Allen953/HotDog/1.3D model/HotDog/LB_SHANK_LINK.SLDASM

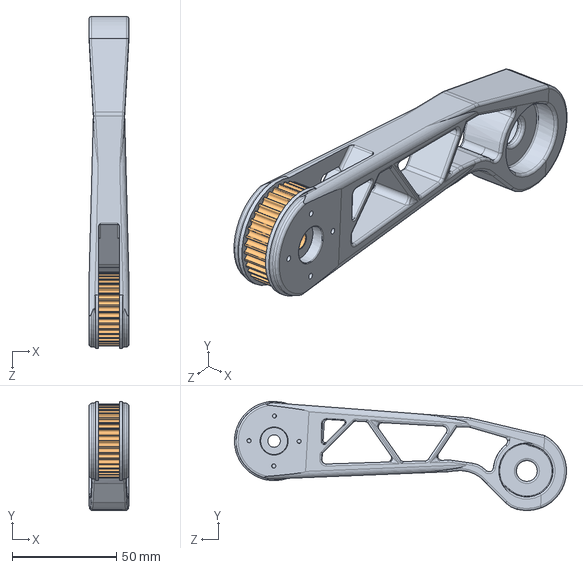
[picture p50: CAD file, 2022-09-22]
1.3D model/HotDog/LB_SHANK_LINK.SLDASM
19.0 x 52.3 x 159.1 mm
小足
同步轮
