Allen953/HotDog/1.3D model/HotDog/LB_THIGH_LINK.SLDASM

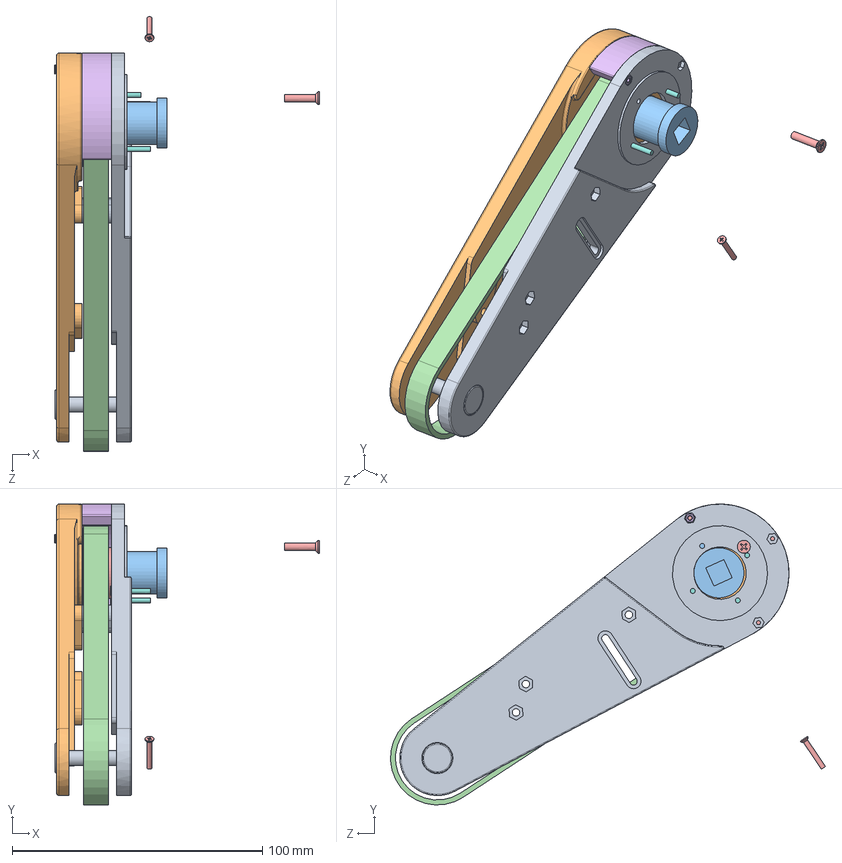
[picture p51: CAD file, 2022-09-22]
1.3D model/HotDog/LB_THIGH_LINK.SLDASM
105.9 x 120.3 x 173.9 mm
大足
大足2
光杆同步轮
同步带
cross recessed countersunk head screws gb1 x 5
hex nuts, style 1-grades ab gb
端盖
cross countersunk head screw_as x 4
字母钉
17-23-4轴承 x 2
传动轴
定位环_17_20_1-2mm
定位环
支撑半环
