Allen953/HotDog/1.3D model/HotDog/定位环_17_20_1-2mm.SLDPRT

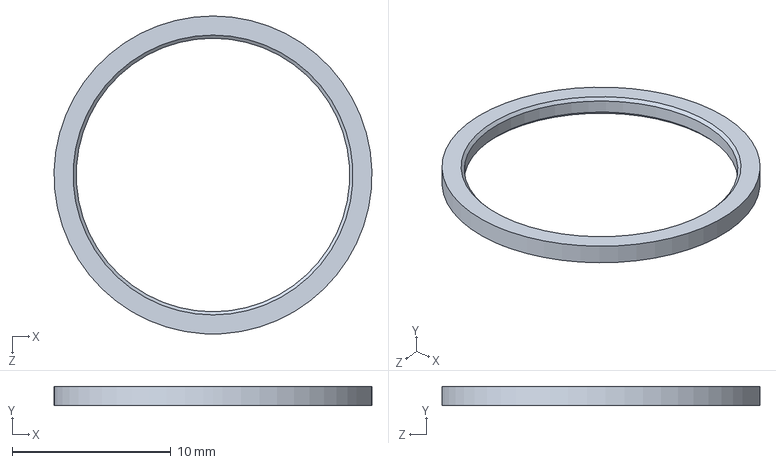
[picture p52: CAD file, 2022-09-22]
1.3D model/HotDog/定位环_17_20_1-2mm.SLDPRT
20.0 x 1.20 x 20.0 mm
