Allen953/HotDog/3.Software/ROS package/HotDog/meshes/LF_R_LINK.STL

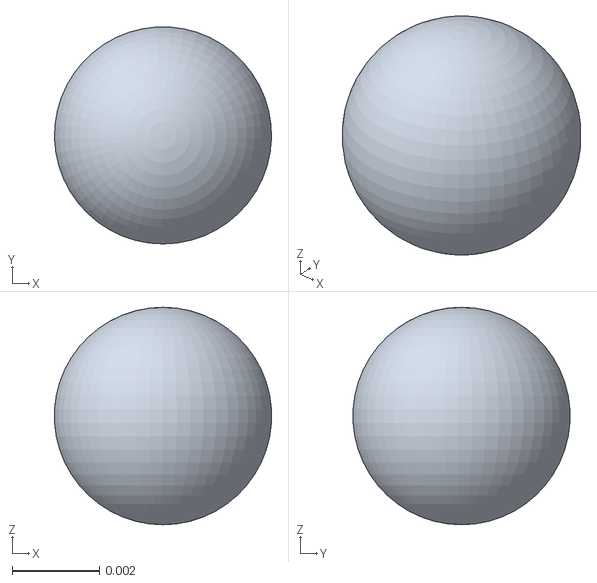
[picture p53: CAD file, 2022-09-22]
3.Software/ROS package/HotDog/meshes/LF_R_LINK.STL
0.00499 x 0.00499 x 0.005
