Allen953/HotDog/1.3D model/HotDog/小足.SLDPRT

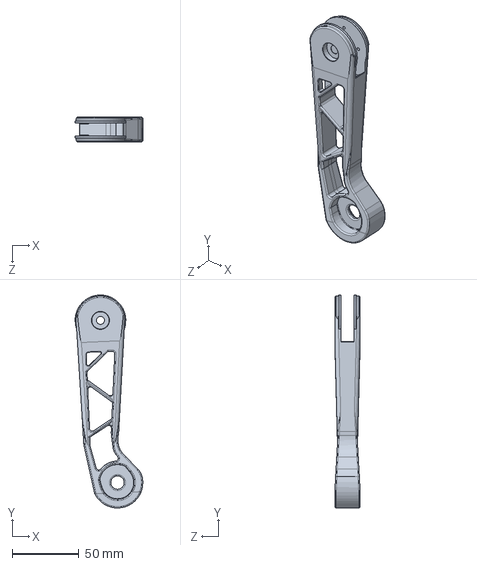
[picture p54: CAD file, 2022-09-22]
1.3D model/HotDog/小足.SLDPRT
50.7 x 159.3 x 19.0 mm
