Allen953/HotDog/3.Software/ROS package/HotDog/meshes/RB_JIAN_LINK.STL

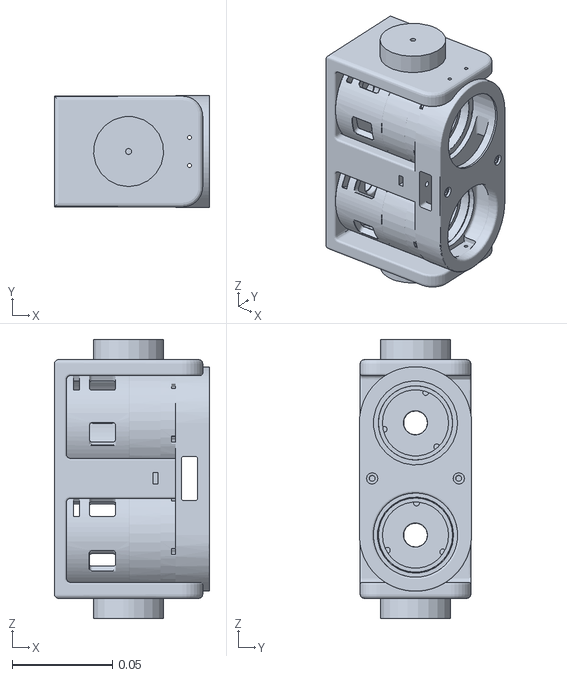
[picture p55: CAD file, 2022-09-22]
3.Software/ROS package/HotDog/meshes/RB_JIAN_LINK.STL
0.0774 x 0.056 x 0.139
