Allen953/HotDog/1.3D model/HotDog/定位环.SLDPRT

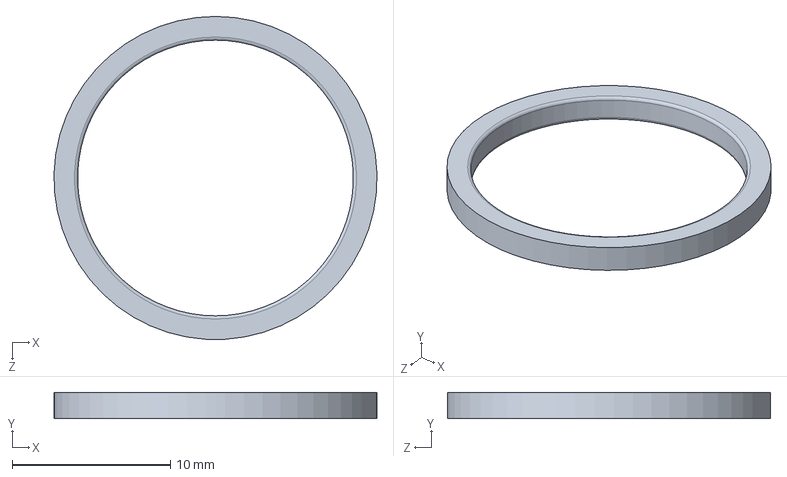
[picture p56: CAD file, 2022-09-22]
1.3D model/HotDog/定位环.SLDPRT
20.4 x 1.65 x 20.4 mm
