Allen953/HotDog/3.Software/ROS package/HotDog/meshes/LB_THIGH_LINK.STL

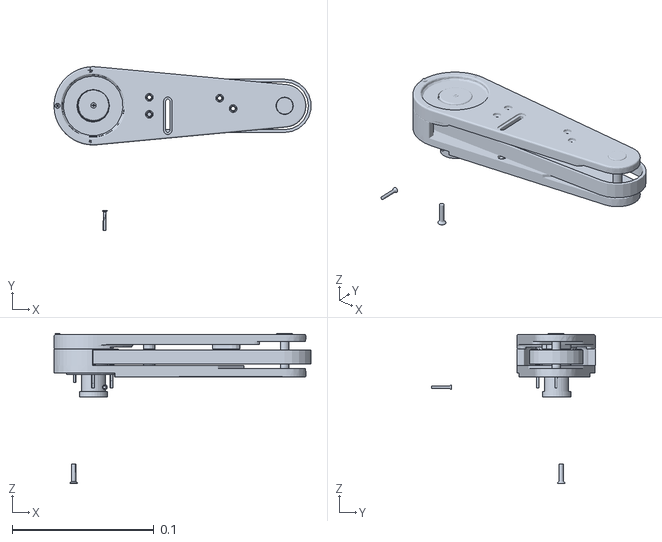
[picture p57: CAD file, 2022-09-22]
3.Software/ROS package/HotDog/meshes/LB_THIGH_LINK.STL
0.181 x 0.115 x 0.106
