Allen953/HotDog/3.Software/ROS package/HotDog/meshes/RB_THIGH_LINK.STL

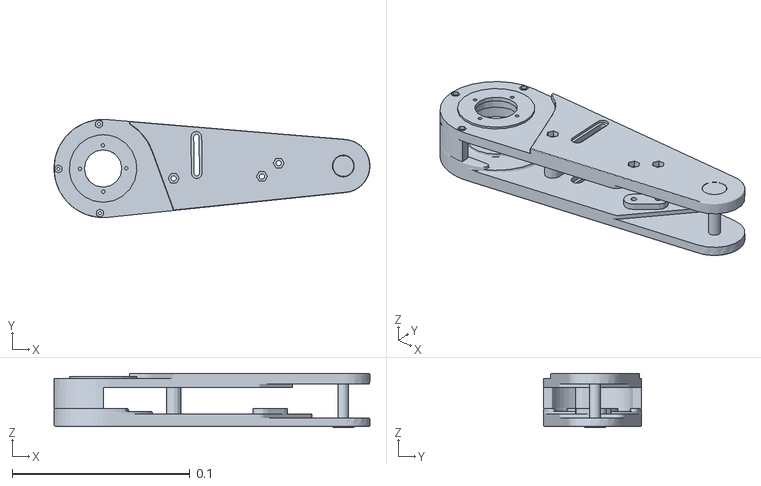
[picture p58: CAD file, 2022-09-22]
3.Software/ROS package/HotDog/meshes/RB_THIGH_LINK.STL
0.178 x 0.0552 x 0.0306
