Allen953/HotDog/1.3D model/HotDog/电机座.SLDPRT

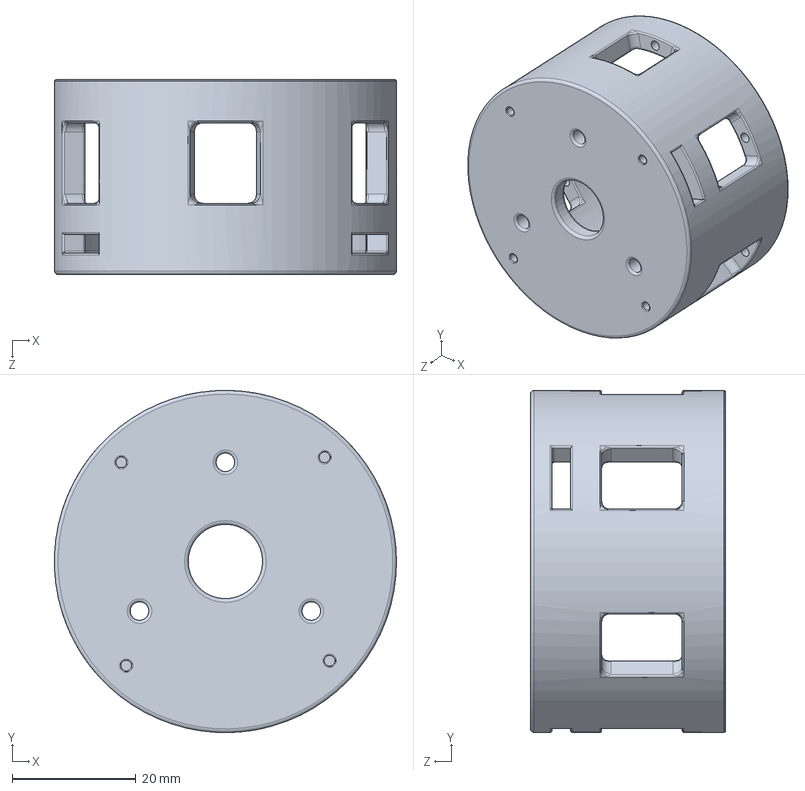
[picture p59: CAD file, 2022-09-22]
1.3D model/HotDog/电机座.SLDPRT
55.2 x 55.2 x 31.5 mm
