Allen953/HotDog/1.3D model/HotDog/碳纤维杆10mm.SLDPRT

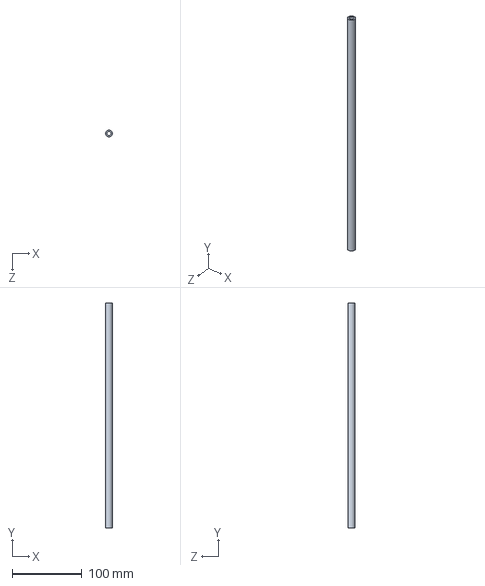
[picture p60: CAD file, 2022-09-22]
1.3D model/HotDog/碳纤维杆10mm.SLDPRT
10.0 x 323.0 x 10.0 mm
