Allen953/HotDog/1.3D model/HotDog/保持架.SLDPRT

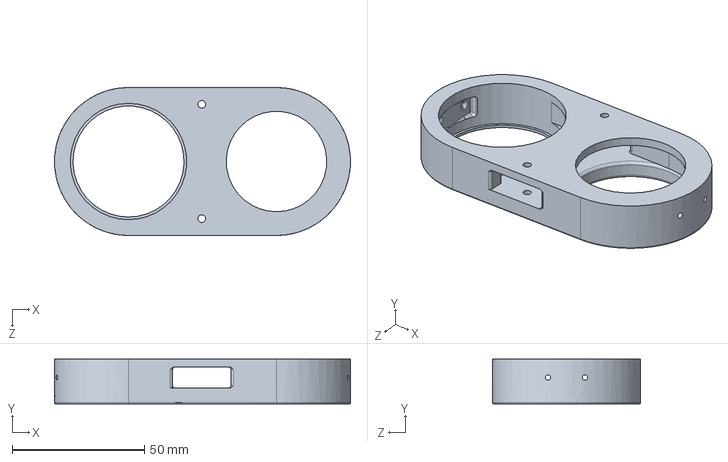
[picture p61: CAD file, 2022-09-22]
1.3D model/HotDog/保持架.SLDPRT
112.0 x 17.0 x 56.0 mm
