Allen953/HotDog/3.Software/ROS package/HotDog/meshes/RB_SHANK_LINK.STL

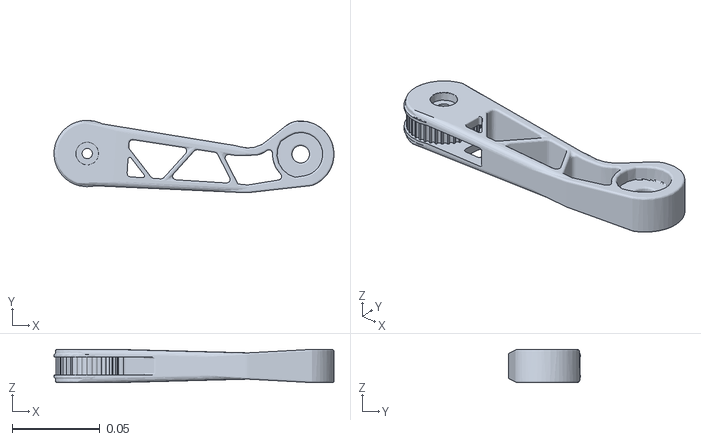
[picture p62: CAD file, 2022-09-22]
3.Software/ROS package/HotDog/meshes/RB_SHANK_LINK.STL
0.16 x 0.0414 x 0.019
