Allen953/HotDog/1.3D model/HotDog/2020铝-70.SLDPRT

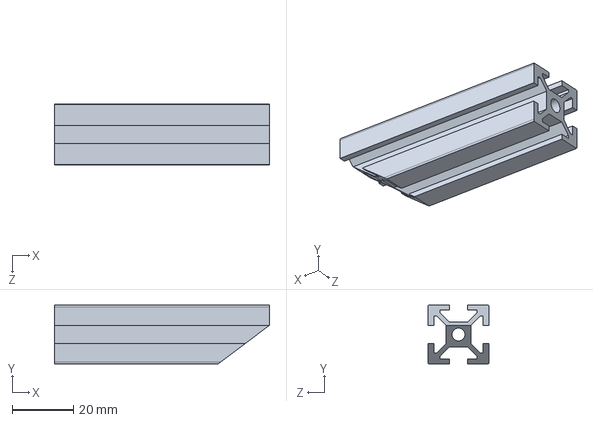
[picture p63: CAD file, 2022-09-22]
1.3D model/HotDog/2020铝-70.SLDPRT
70.0 x 19.2 x 20.0 mm
