Allen953/HotDog/1.3D model/HotDog/固定桁架.SLDPRT

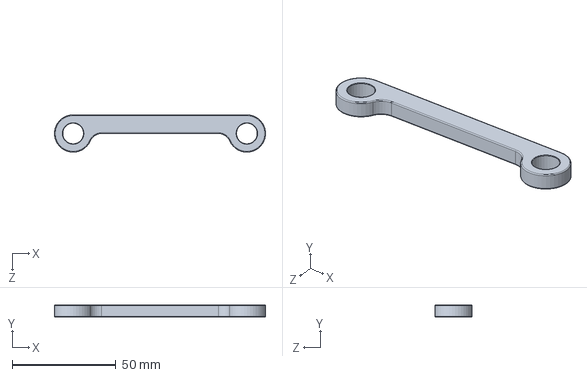
[picture p64: CAD file, 2022-09-22]
1.3D model/HotDog/固定桁架.SLDPRT
101.6 x 6.00 x 18.0 mm
