Allen953/HotDog/1.3D model/HotDog/后端板.SLDPRT

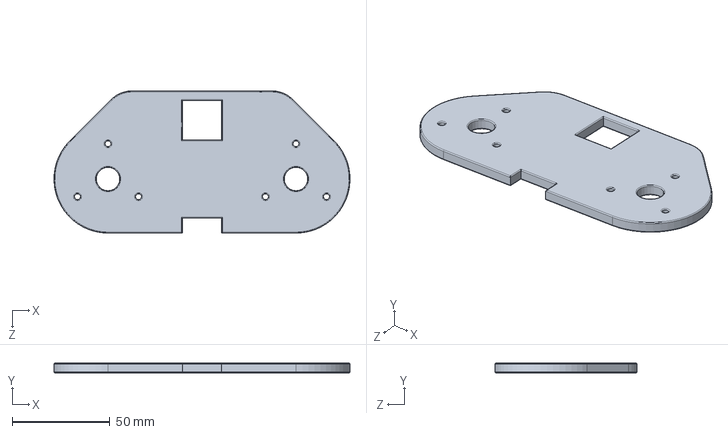
[picture p65: CAD file, 2022-09-22]
1.3D model/HotDog/后端板.SLDPRT
151.2 x 5.00 x 72.6 mm
