Allen953/HotDog/1.3D model/HotDog/111.SLDPRT

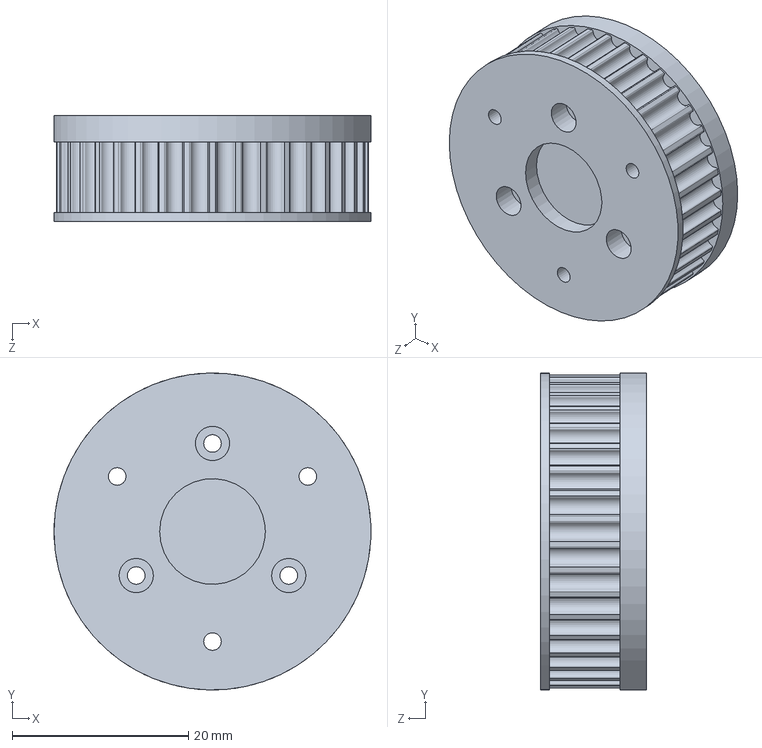
[picture p66: CAD file, 2022-09-22]
1.3D model/HotDog/111.SLDPRT
36.0 x 36.0 x 12.0 mm
