Allen953/HotDog/1.3D model/HotDog/身躯架1.SLDPRT

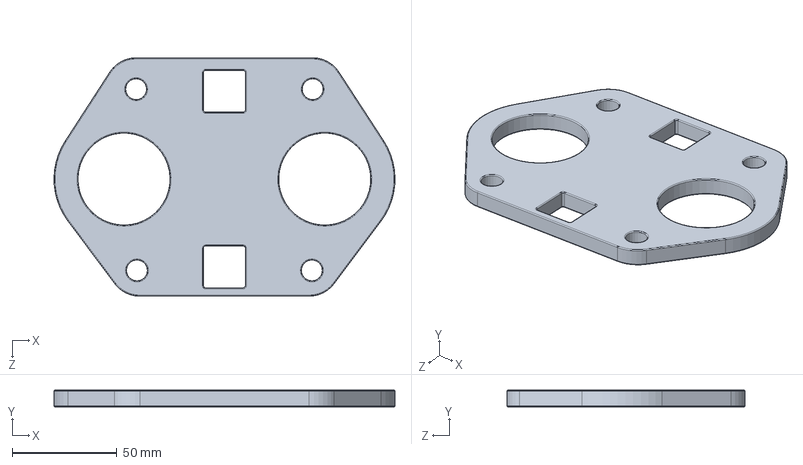
[picture p68: CAD file, 2022-09-22]
1.3D model/HotDog/身躯架1.SLDPRT
163.1 x 8.00 x 114.0 mm
