Allen953/HotDog/3.Software/ROS package/HotDog/meshes/RF_JIAN_LINK.STL

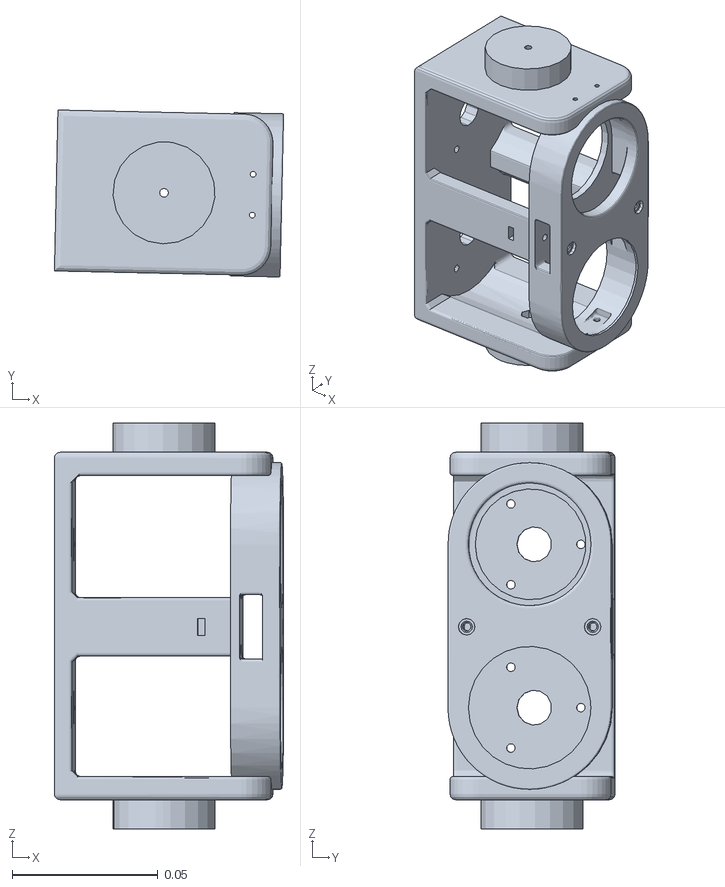
[picture p69: CAD file, 2022-09-22]
3.Software/ROS package/HotDog/meshes/RF_JIAN_LINK.STL
0.0786 x 0.0573 x 0.139
