Allen953/HotDog/1.3D model/HotDog/35-44-5轴承.SLDPRT

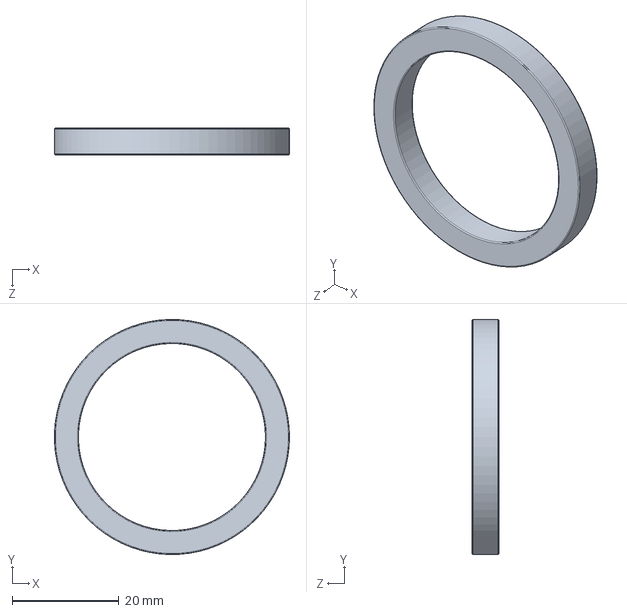
[picture p70: CAD file, 2022-09-22]
1.3D model/HotDog/35-44-5轴承.SLDPRT
44.0 x 44.0 x 5.00 mm
