Allen953/HotDog/1.3D model/HotDog/电机46.SLDPRT

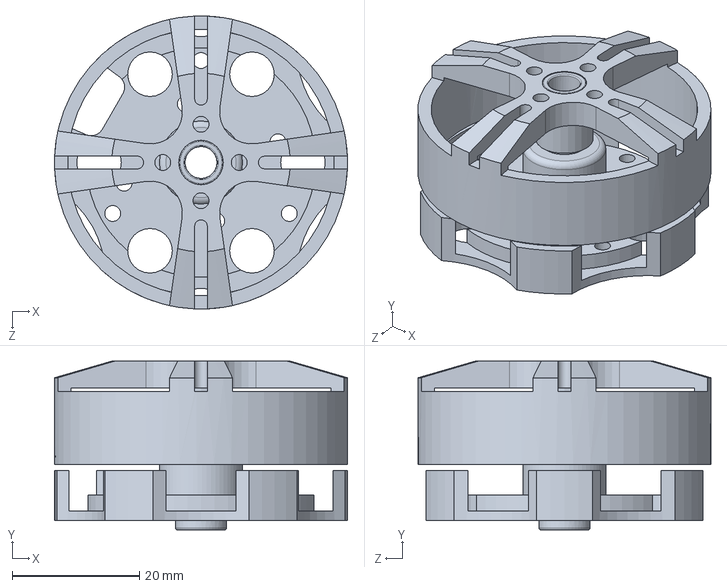
[picture p72: CAD file, 2022-09-22]
1.3D model/HotDog/电机46.SLDPRT
46.0 x 26.5 x 46.0 mm
