Allen953/HotDog/1.3D model/HotDog/光杆同步轮.SLDPRT

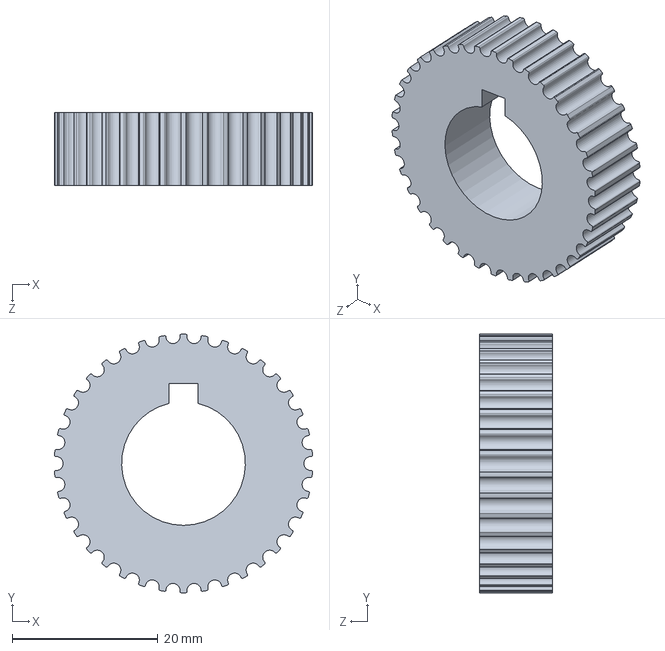
[picture p73: CAD file, 2022-09-22]
1.3D model/HotDog/光杆同步轮.SLDPRT
35.4 x 35.5 x 10.0 mm
