Allen953/HotDog/1.3D model/HotDog/同步带.SLDPRT

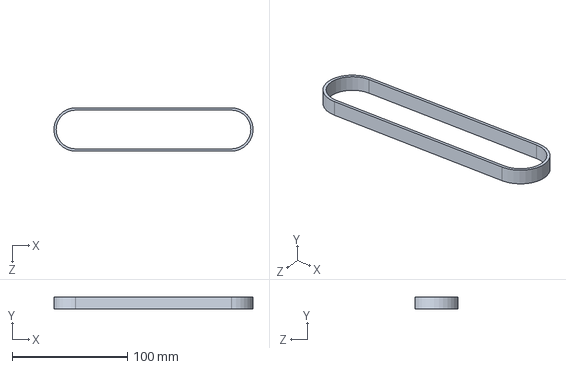
[picture p74: CAD file, 2022-09-22]
1.3D model/HotDog/同步带.SLDPRT
172.3 x 10.0 x 37.5 mm
