Allen953/HotDog/1.3D model/HotDog/减速器壳体.SLDPRT

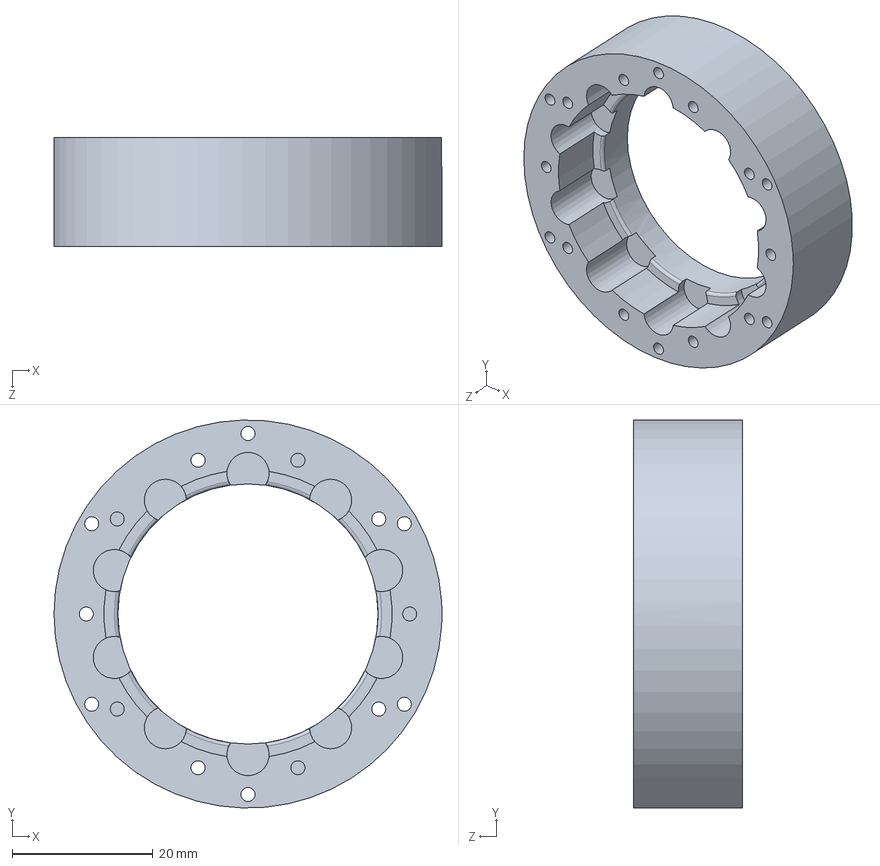
[picture p75: CAD file, 2022-09-22]
1.3D model/HotDog/减速器壳体.SLDPRT
55.2 x 55.2 x 15.5 mm
