Allen953/HotDog/1.3D model/HotDog/传动轴.SLDPRT

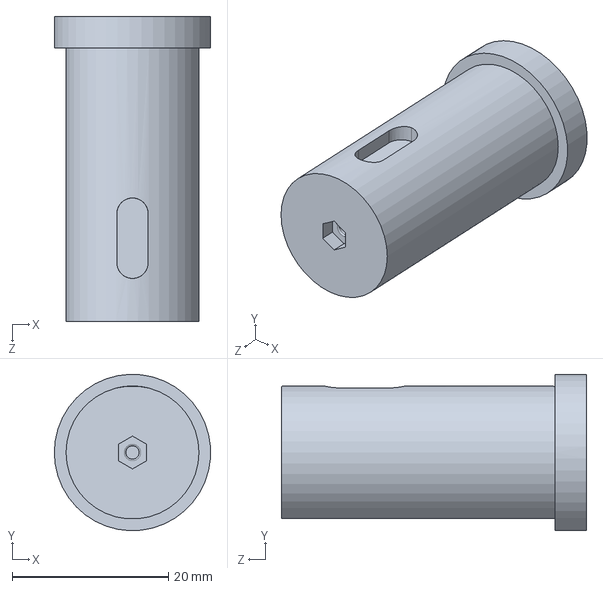
[picture p77: CAD file, 2022-09-22]
1.3D model/HotDog/传动轴.SLDPRT
20.0 x 20.0 x 39.0 mm
