Allen953/HotDog/3.Software/ROS package/HotDog/meshes/LB_SHANK_LINK.STL

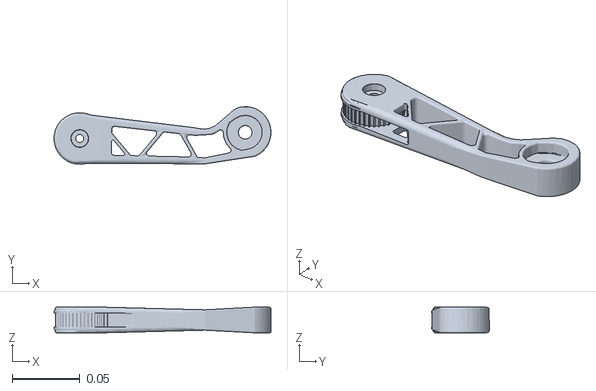
[picture p78: CAD file, 2022-09-22]
3.Software/ROS package/HotDog/meshes/LB_SHANK_LINK.STL
0.16 x 0.0424 x 0.019
