Allen953/HotDog/1.3D model/HotDog/17-23-4轴承.SLDPRT

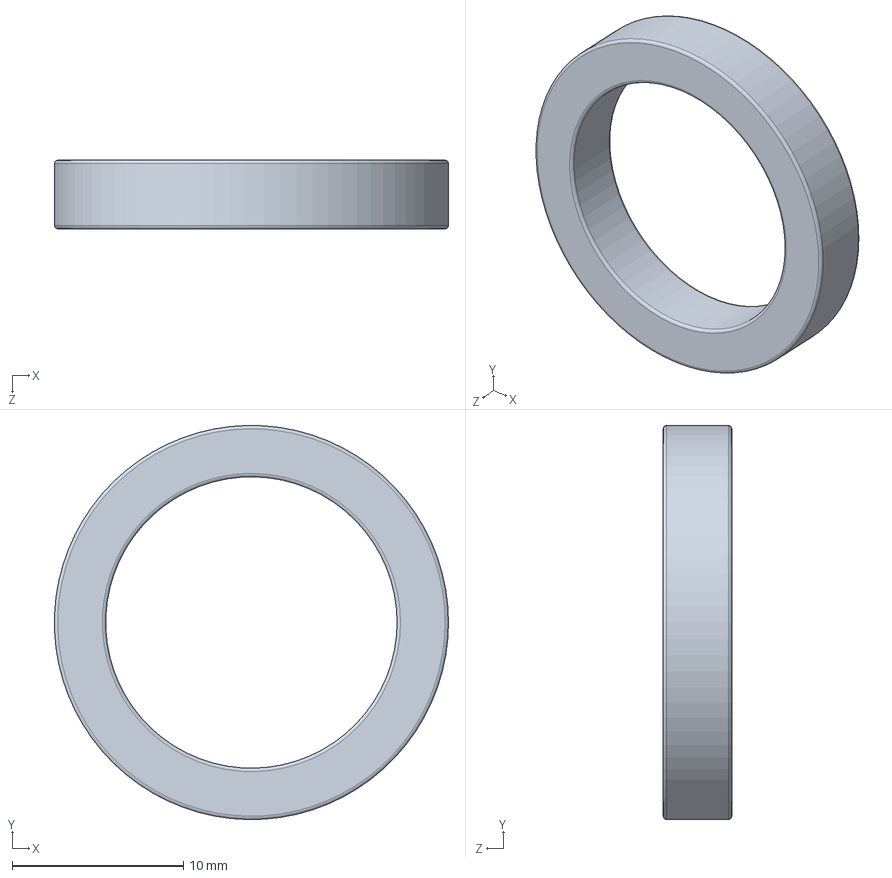
[picture p81: CAD file, 2022-09-22]
1.3D model/HotDog/17-23-4轴承.SLDPRT
23.0 x 23.0 x 4.00 mm
