Allen953/HotDog/1.3D model/HotDog/大足2.SLDPRT

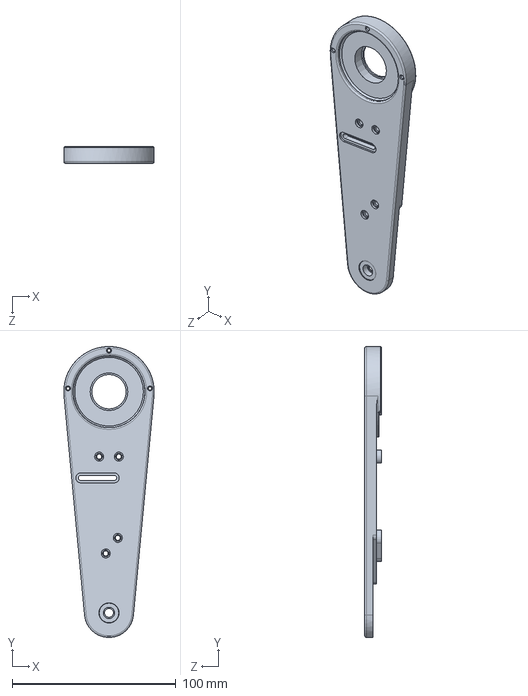
[picture p82: CAD file, 2022-09-22]
1.3D model/HotDog/大足2.SLDPRT
55.2 x 177.6 x 10.2 mm
