Allen953/HotDog/1.3D model/HotDog/输出轴.SLDPRT

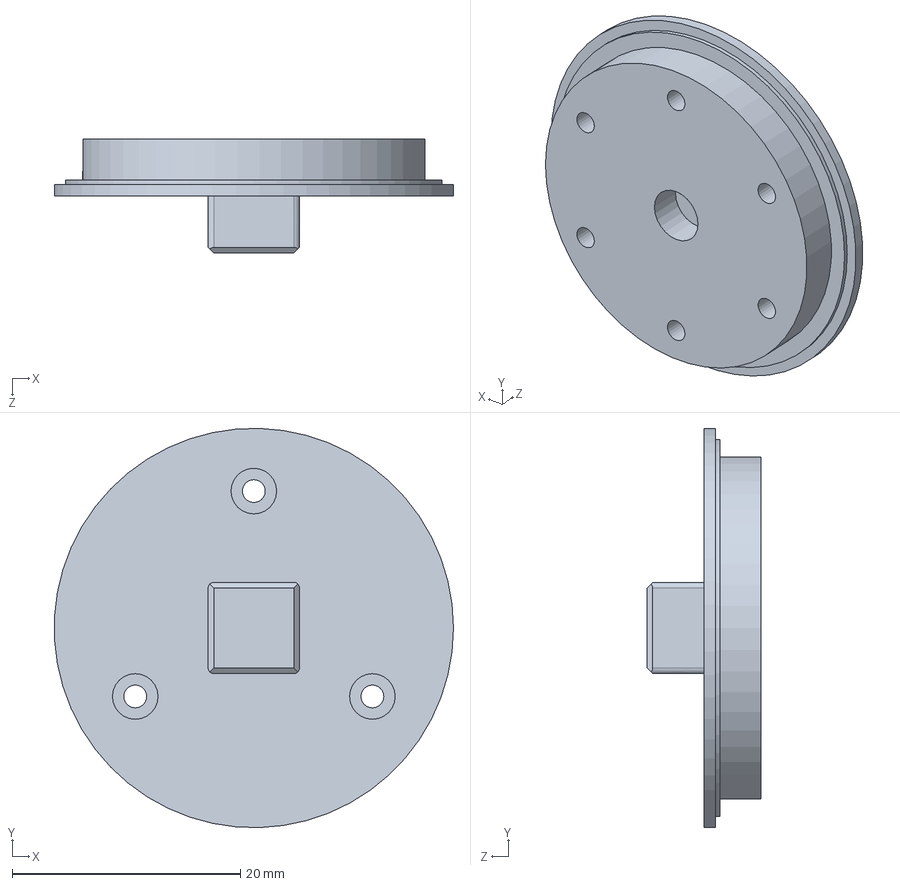
[picture p83: CAD file, 2022-09-22]
1.3D model/HotDog/输出轴.SLDPRT
35.0 x 35.0 x 10.0 mm
