Allen953/HotDog/1.3D model/HotDog/减速器上盖.SLDPRT

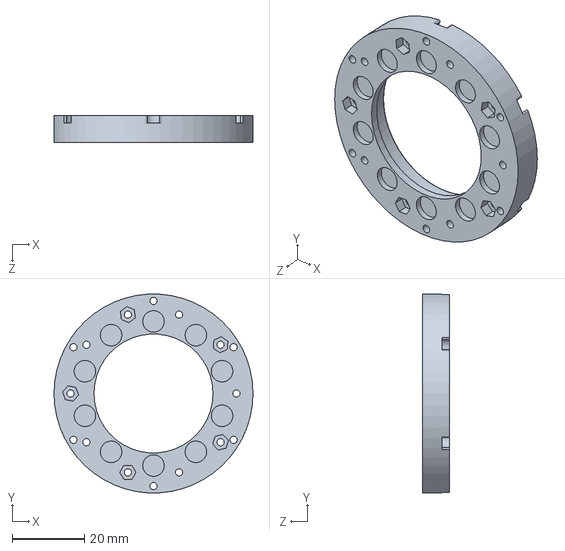
[picture p84: CAD file, 2022-09-22]
1.3D model/HotDog/减速器上盖.SLDPRT
55.2 x 55.1 x 7.40 mm
