Allen953/HotDog/1.3D model/HotDog/大足.SLDPRT

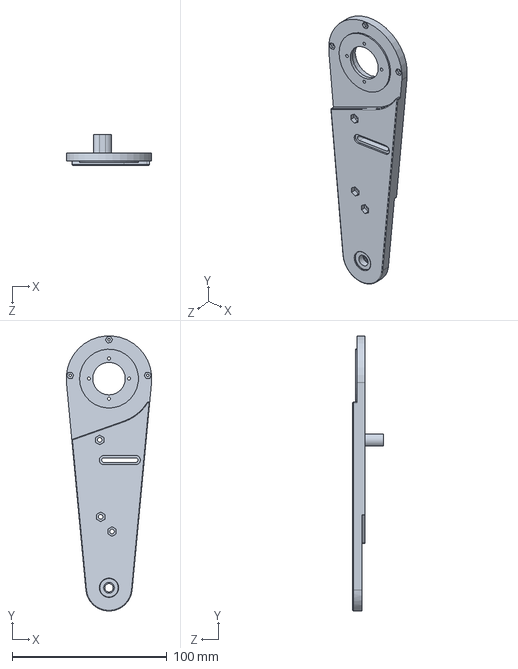
[picture p85: CAD file, 2022-09-22]
1.3D model/HotDog/大足.SLDPRT
55.0 x 177.5 x 19.8 mm
