Allen953/HotDog/1.3D model/HotDog/NFS5-2020-360.0.SLDPRT

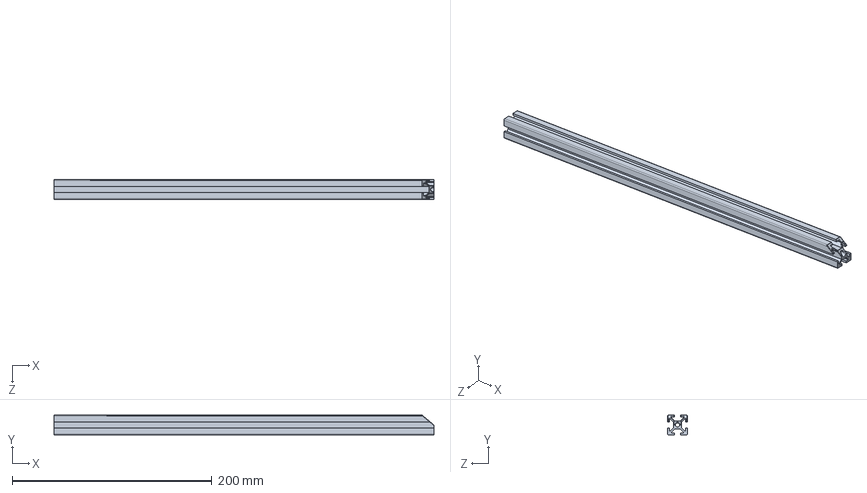
[picture p86: CAD file, 2022-09-22]
1.3D model/HotDog/NFS5-2020-360.0.SLDPRT
380.0 x 20.0 x 20.0 mm
