Allen953/HotDog/1.3D model/HotDog/支撑半环.SLDPRT

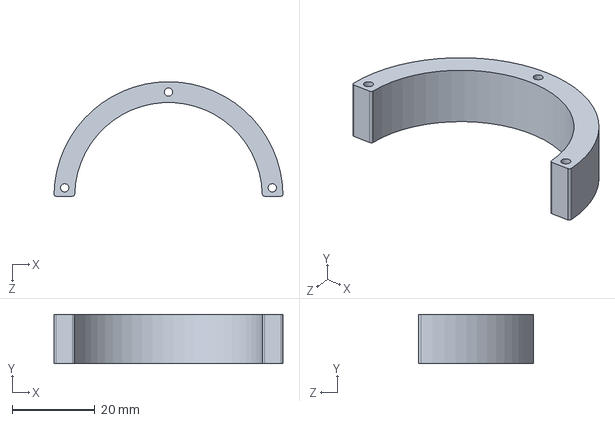
[picture p87: CAD file, 2022-09-22]
1.3D model/HotDog/支撑半环.SLDPRT
55.2 x 11.9 x 27.6 mm
