Allen953/HotDog/1.3D model/HotDog/Virtual_part.SLDPRT

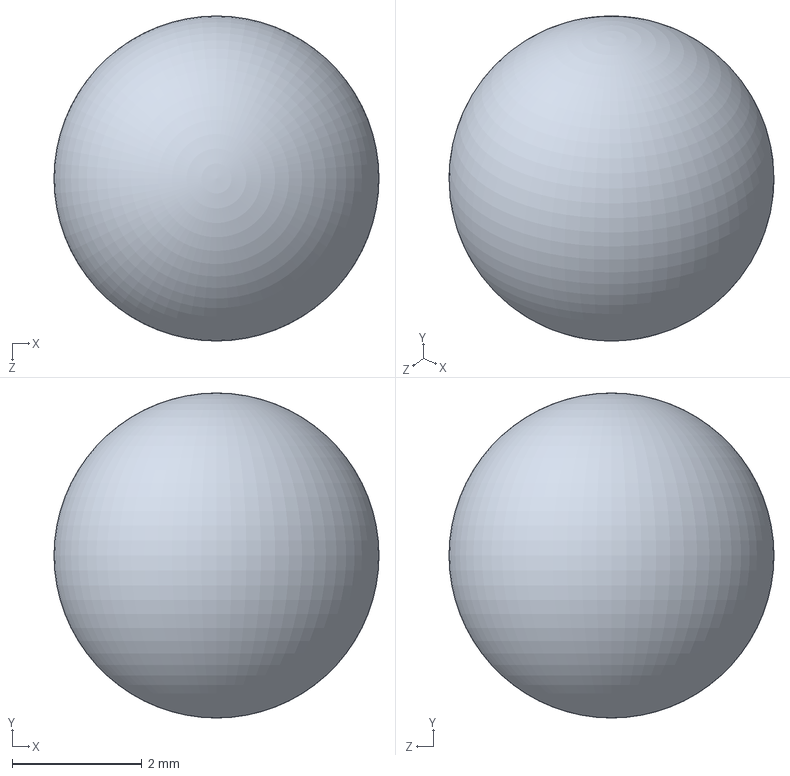
[picture p88: CAD file, 2022-09-22]
1.3D model/HotDog/Virtual_part.SLDPRT
5.00 x 5.00 x 5.00 mm
