Allen953/HotDog/1.3D model/HotDog/端盖.SLDPRT

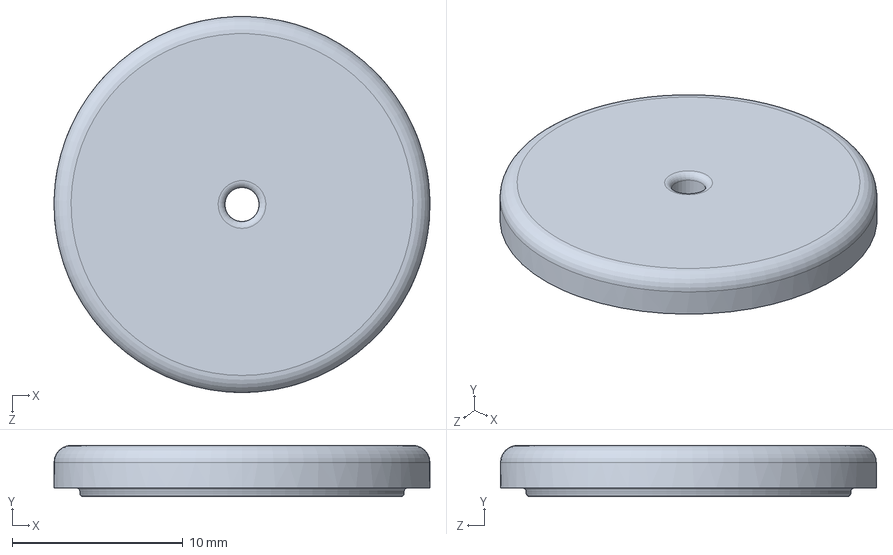
[picture p89: CAD file, 2022-09-22]
1.3D model/HotDog/端盖.SLDPRT
22.0 x 3.00 x 22.0 mm
