Allen953/HotDog/1.3D model/HotDog/30-37-4轴承6.SLDPRT

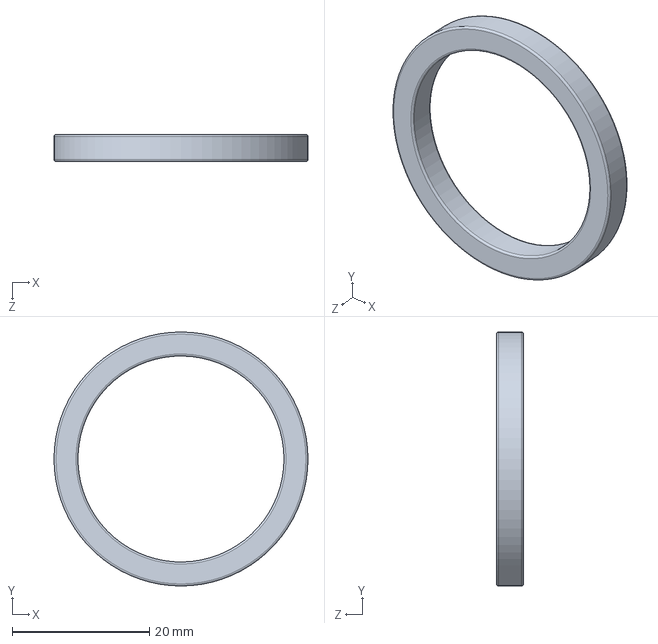
[picture p90: CAD file, 2022-09-22]
1.3D model/HotDog/30-37-4轴承6.SLDPRT
37.0 x 37.0 x 4.00 mm
