Allen953/HotDog/1.3D model/HotDog/同步带168.SLDPRT

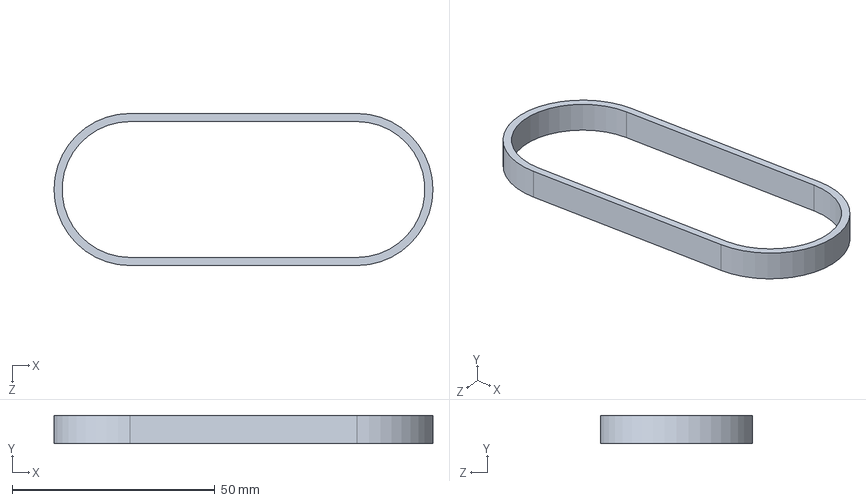
[picture p91: CAD file, 2022-09-22]
1.3D model/HotDog/同步带168.SLDPRT
93.5 x 7.00 x 37.5 mm
