Allen953/HotDog/1.3D model/HotDog/张紧轮.SLDPRT

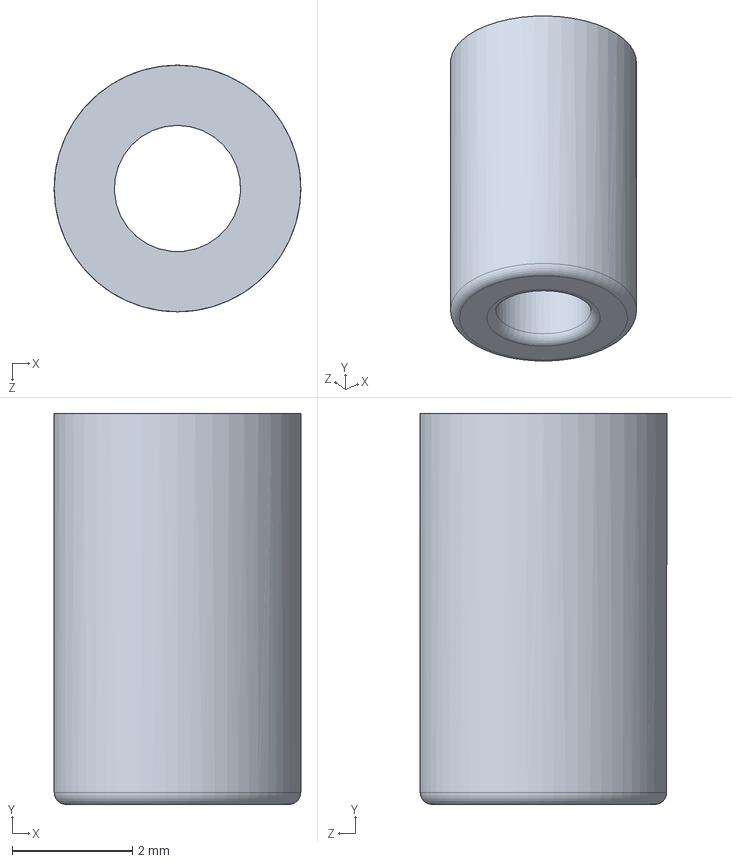
[picture p92: CAD file, 2022-09-22]
1.3D model/HotDog/张紧轮.SLDPRT
4.10 x 6.50 x 4.10 mm
