Allen953/HotDog/1.3D model/HotDog/支撑架.SLDPRT

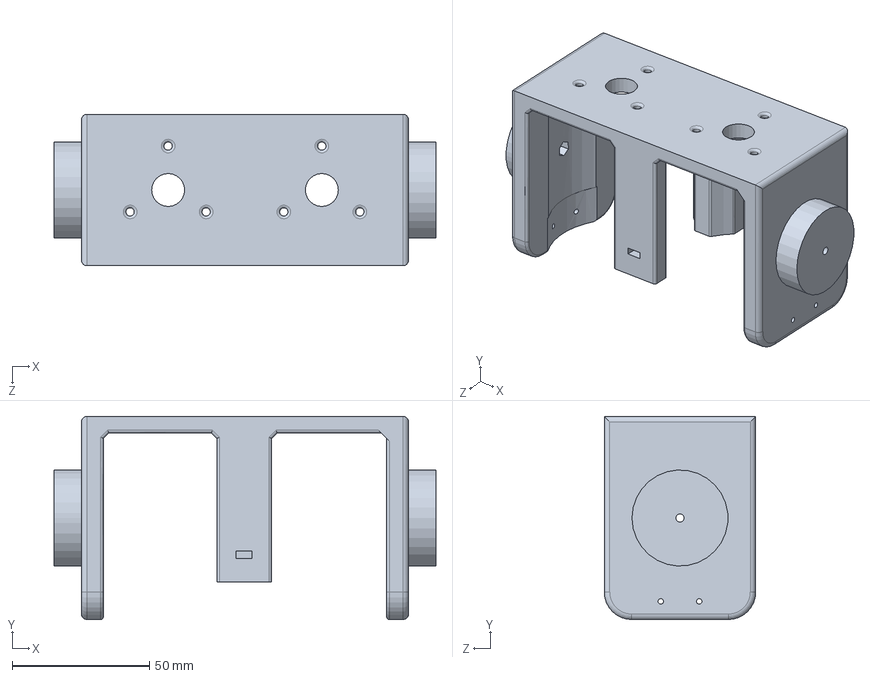
[picture p93: CAD file, 2022-09-22]
1.3D model/HotDog/支撑架.SLDPRT
139.2 x 74.0 x 55.2 mm
