Allen953/HotDog/1.3D model/HotDog/字母钉.SLDPRT

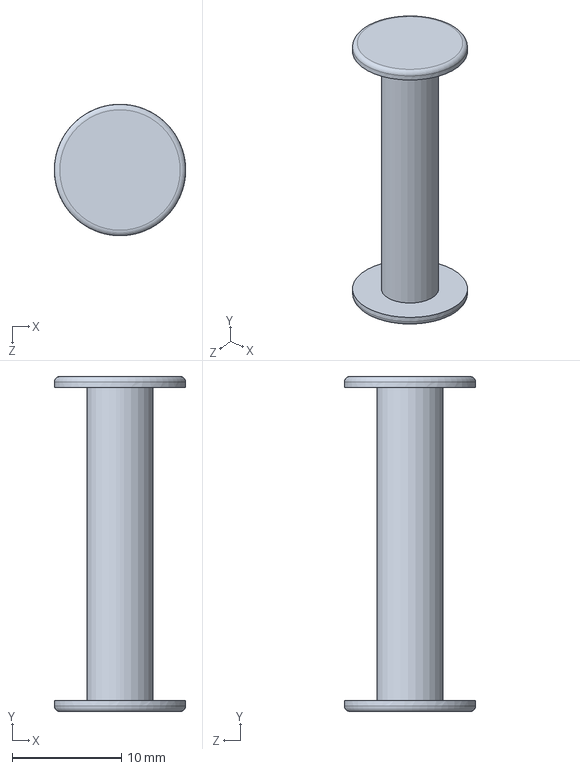
[picture p94: CAD file, 2022-09-22]
1.3D model/HotDog/字母钉.SLDPRT
12.0 x 30.6 x 12.0 mm
