Allen953/HotDog/1.3D model/HotDog/磁铁.SLDPRT

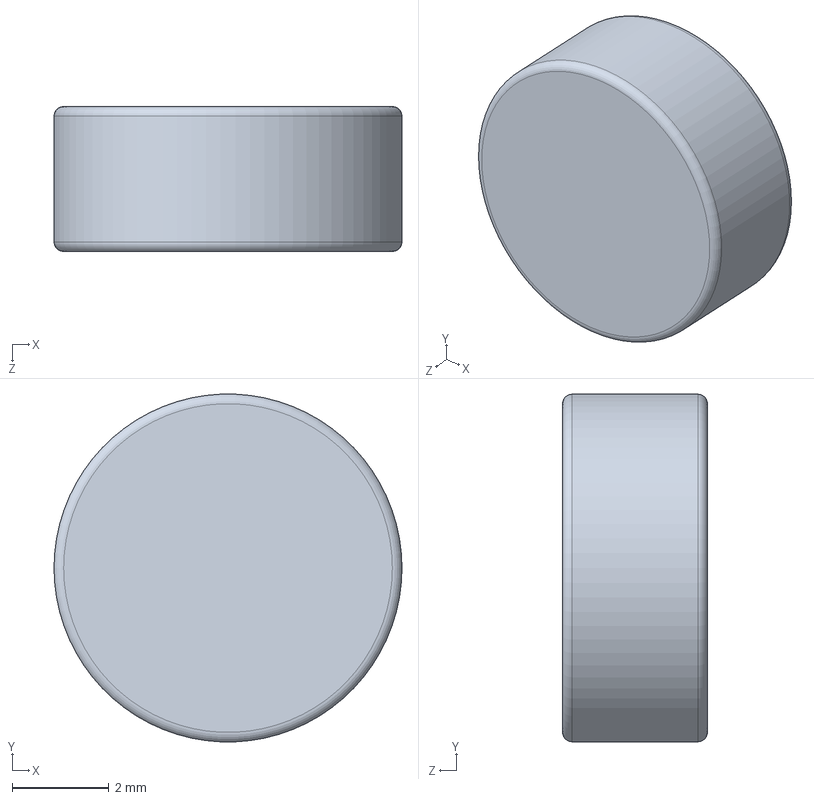
[picture p95: CAD file, 2022-09-22]
1.3D model/HotDog/磁铁.SLDPRT
7.20 x 7.19 x 3.00 mm
